dwblair/open-lab-monitor/pcb/reference/microsdbb_LRG.jpg

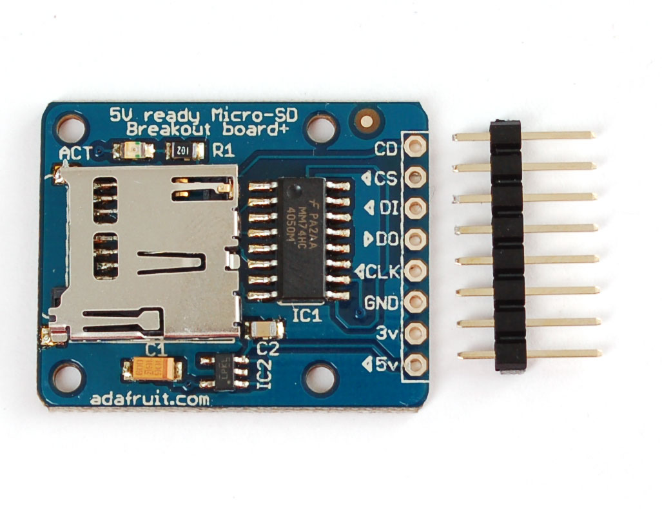
pcb/reference/microsdbb_LRG.jpg
