dwblair/open-lab-monitor/pcb/eagle/olm-base_v0.9brd.png

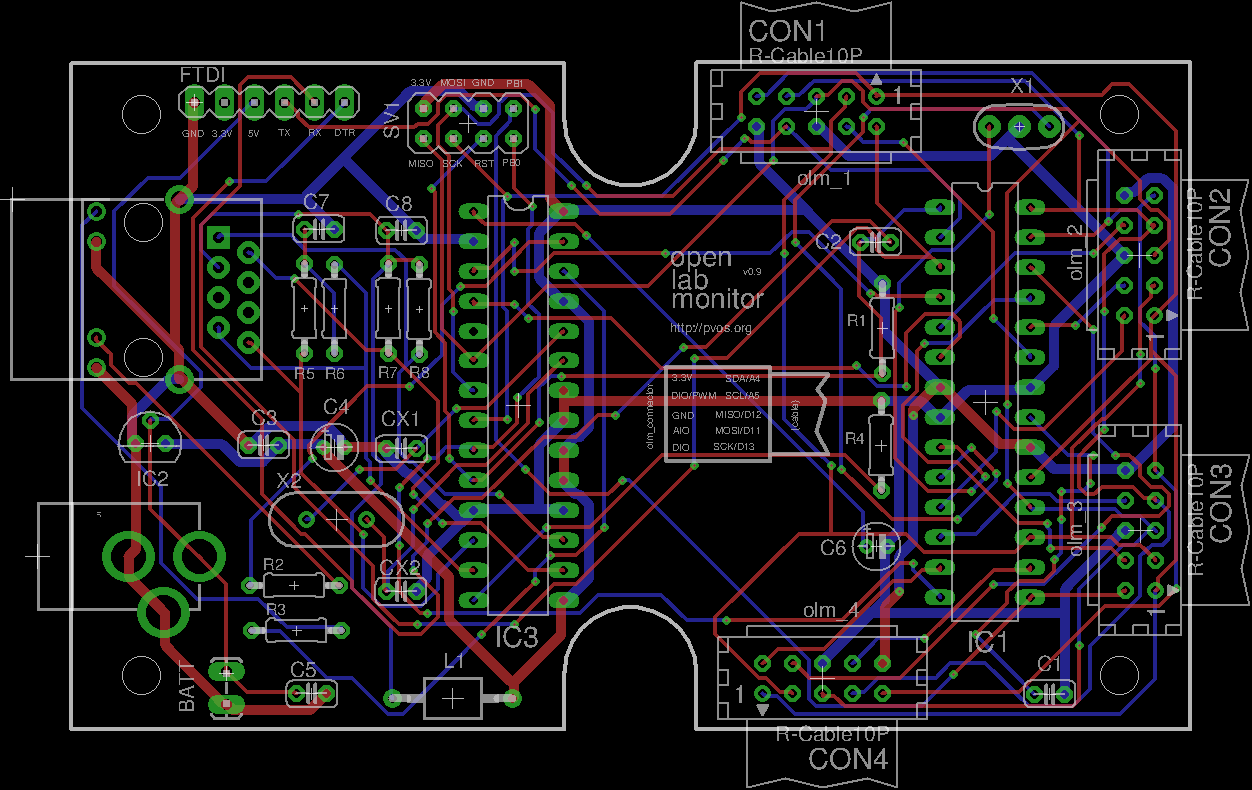
pcb/eagle/olm-base_v0.9brd.png
