dwblair/open-lab-monitor/pcb/eagle/olm-base_v0.9sch.png

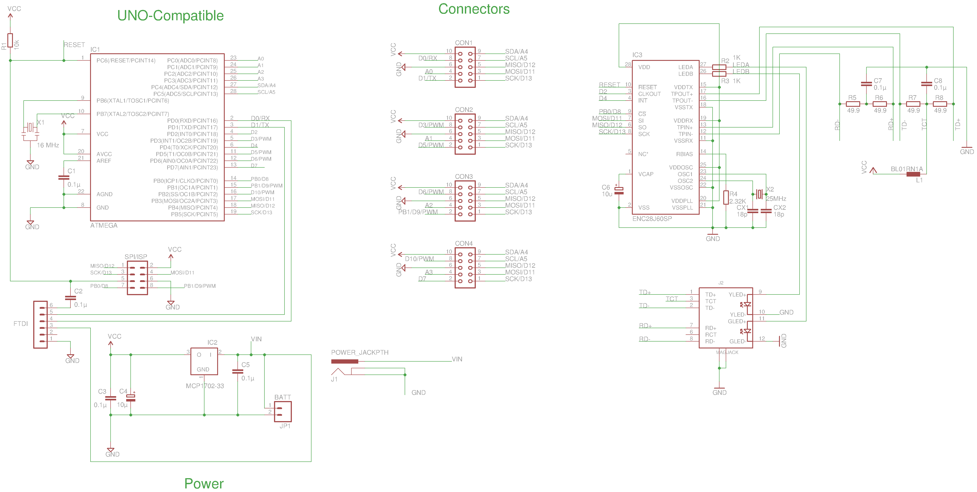
pcb/eagle/olm-base_v0.9sch.png
