dwblair/open-lab-monitor/pcb/eagle/OLM-base_v.9REVA.png

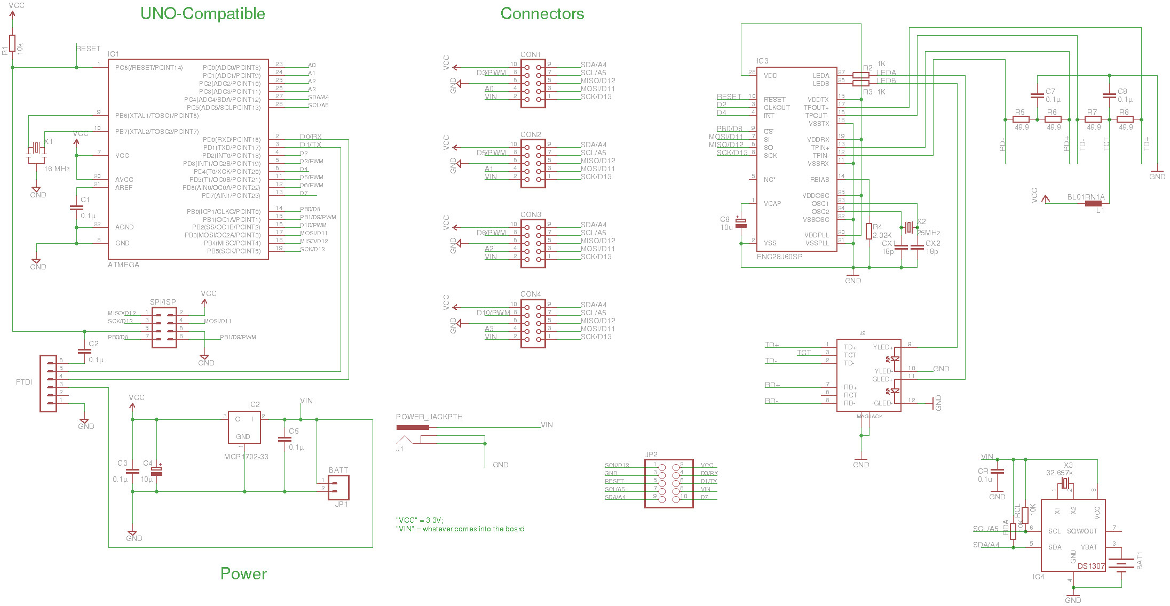
pcb/eagle/OLM-base_v.9REVA.png
