dwblair/open-lab-monitor/pcb/eagle/OLM-base_v.9REVAbrd.png

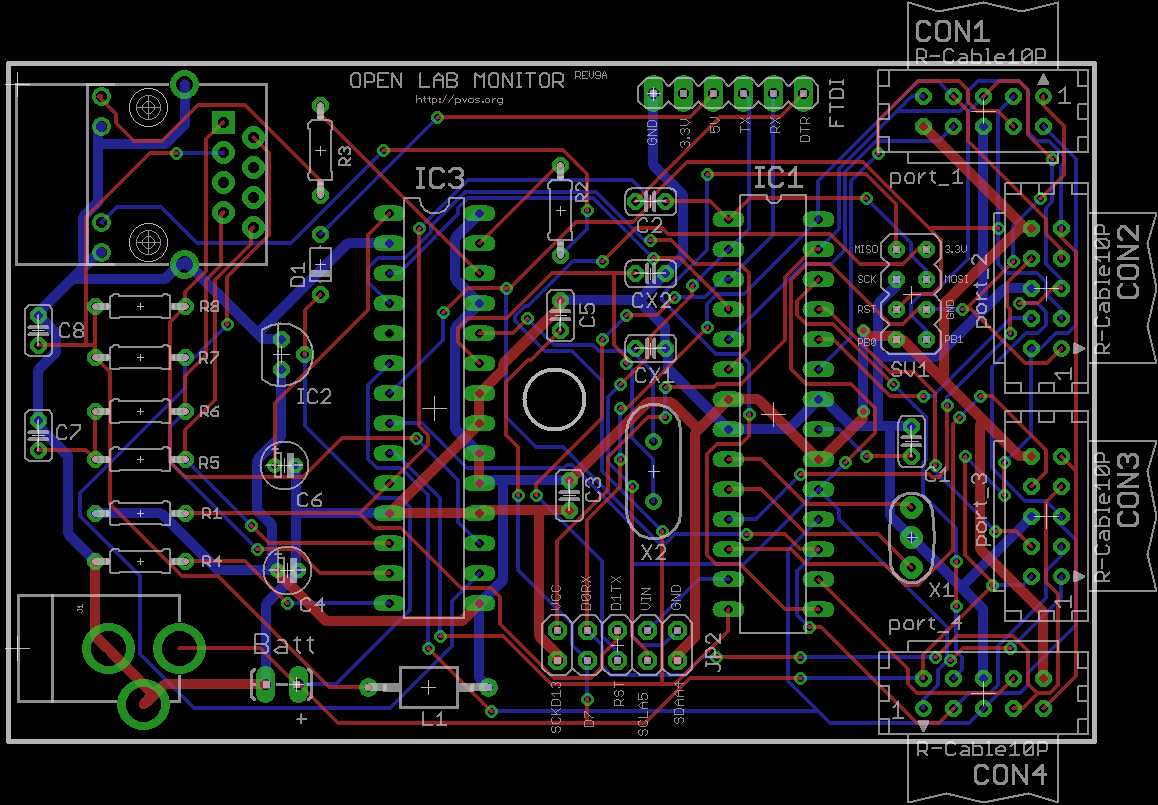
pcb/eagle/OLM-base_v.9REVAbrd.png
