dwblair/open-lab-monitor/pcb/eagle/OLM-base_v.9REVAsch.png

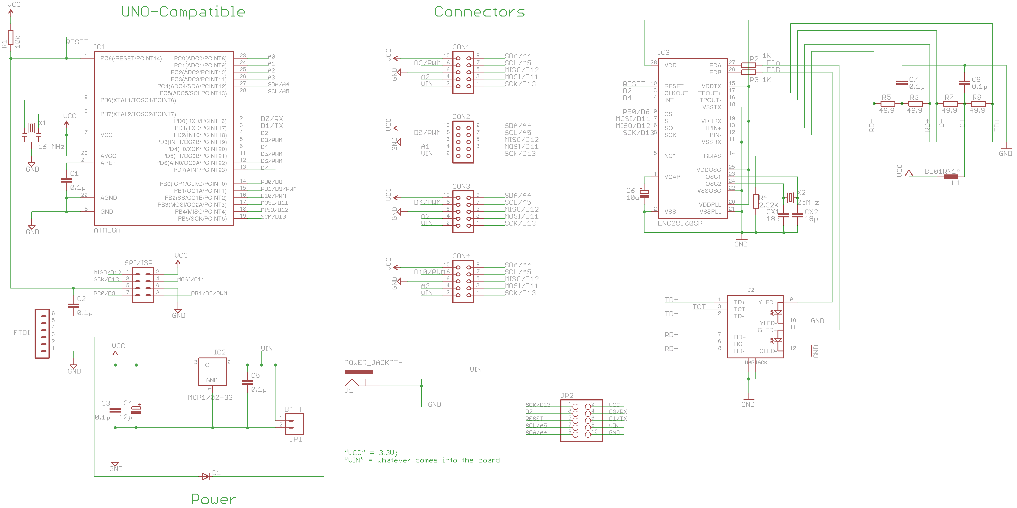
pcb/eagle/OLM-base_v.9REVAsch.png
