dwblair/open-lab-monitor/pcb/eagle/OLM-periph-prob+ambientsch.png

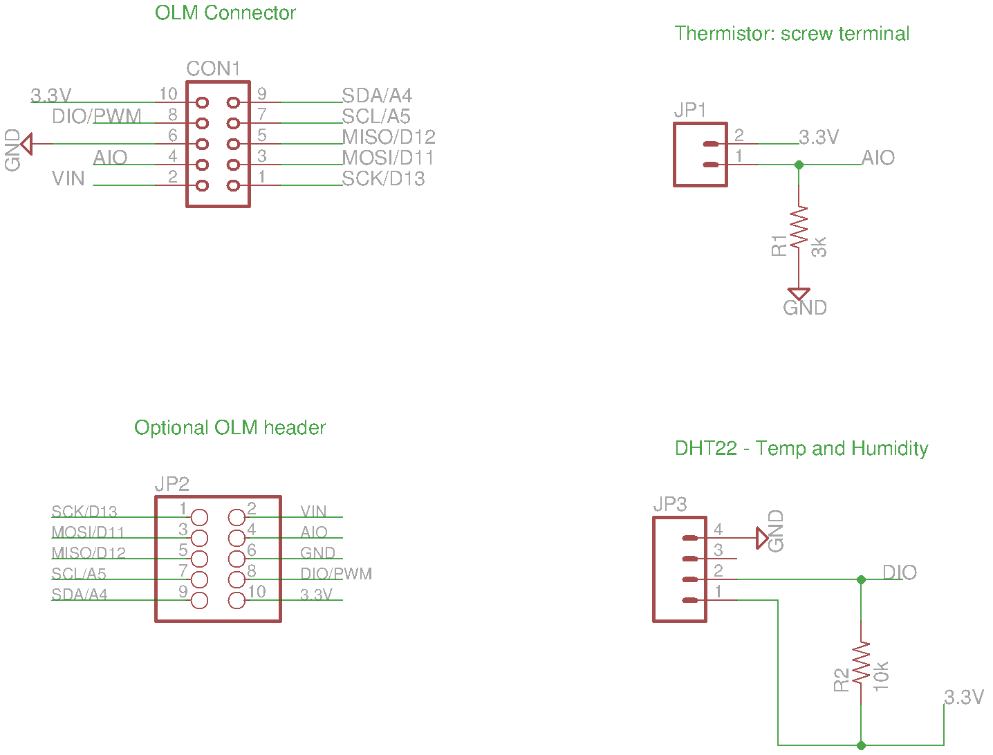
pcb/eagle/OLM-periph-prob+ambientsch.png
