dwblair/open-lab-monitor/pcb/eagle/olm-periph-probe+ambientREV9Abrd.png

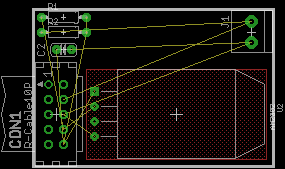
pcb/eagle/olm-periph-probe+ambientREV9Abrd.png
