dwblair/open-lab-monitor/pcb/geda/OLM-v5.png

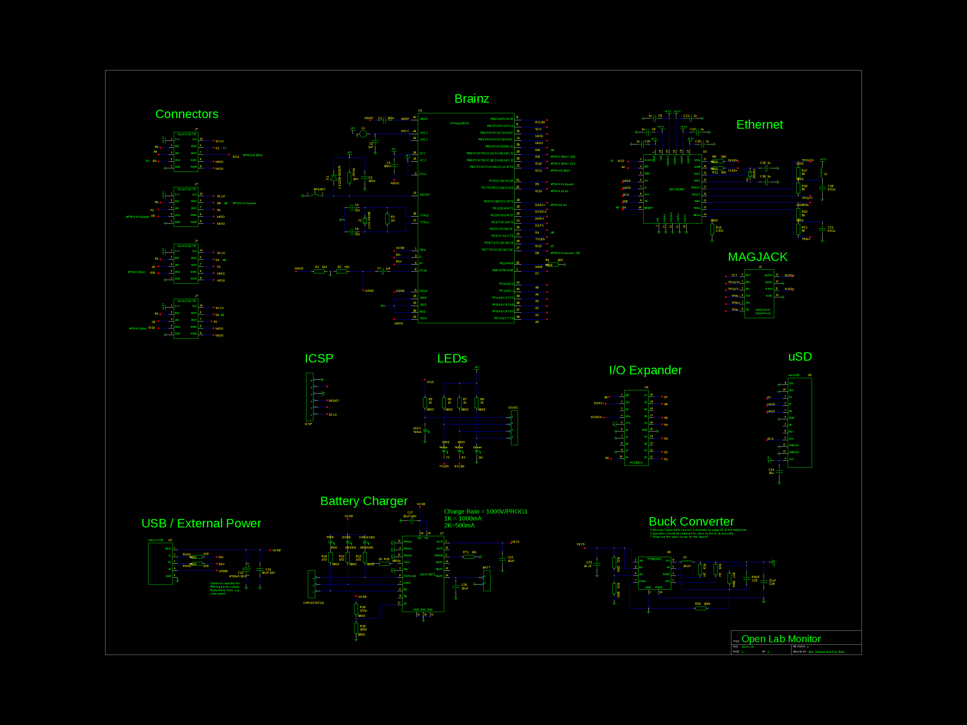
pcb/geda/OLM-v5.png
