dwblair/open-lab-monitor/pcb/reference/OLM.png

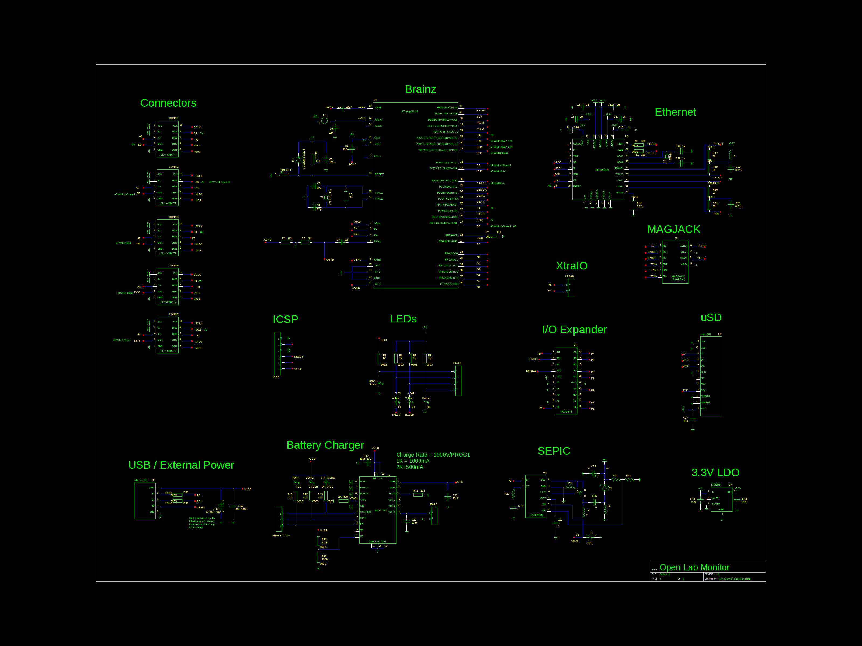
pcb/reference/OLM.png
