dwblair/open-lab-monitor/pcb/reference/olmetherv02.png

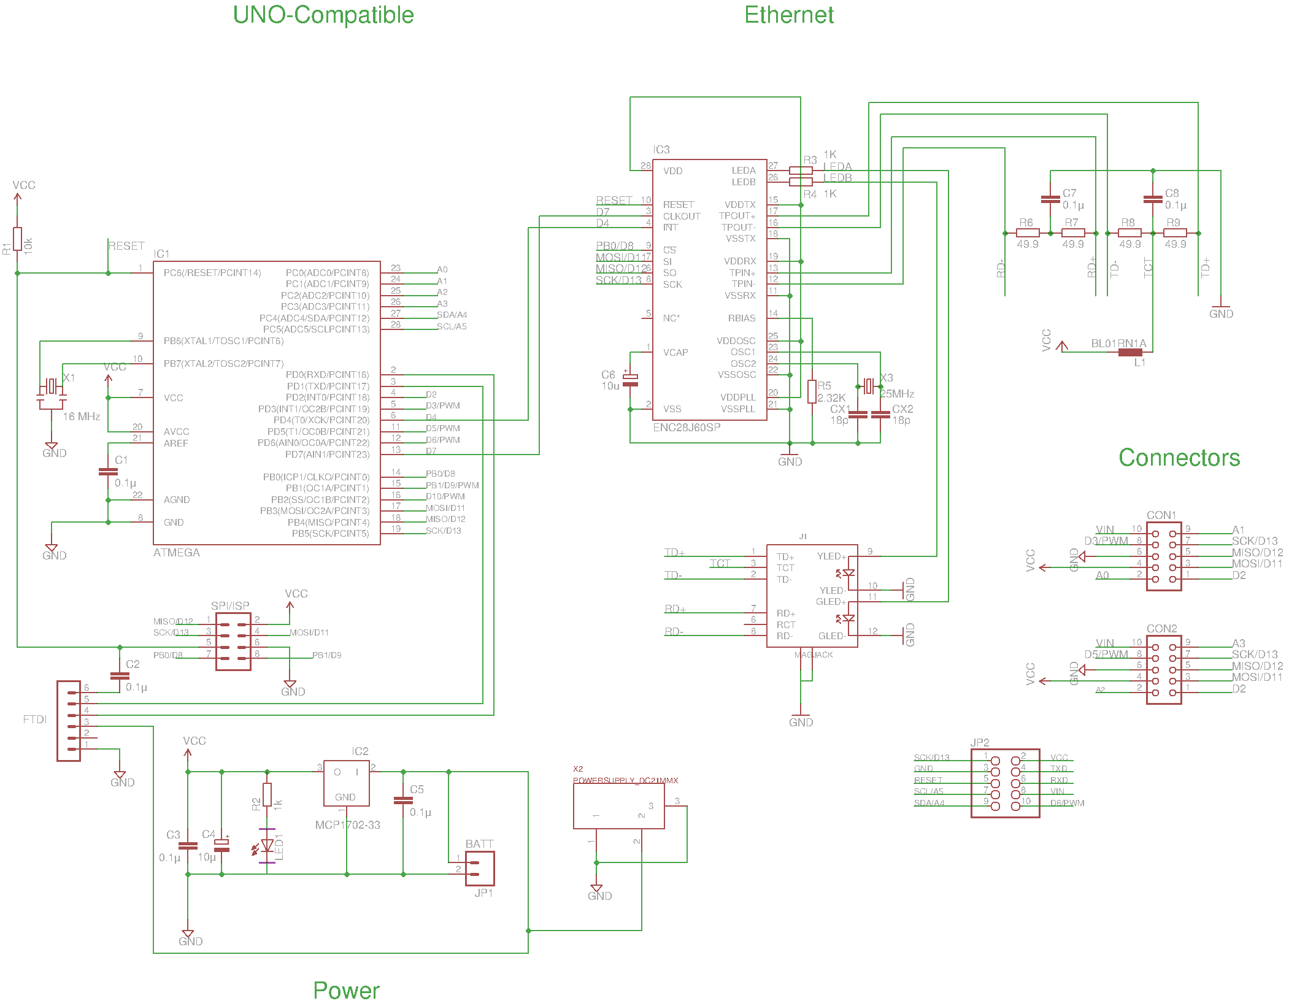
pcb/reference/olmetherv02.png
