dwblair/open-lab-monitor/docs/Arduino_Leonardo-REV3b.brd

## EAGLE design docs/Arduino_Leonardo-REV3b.brd (2013-01-09)

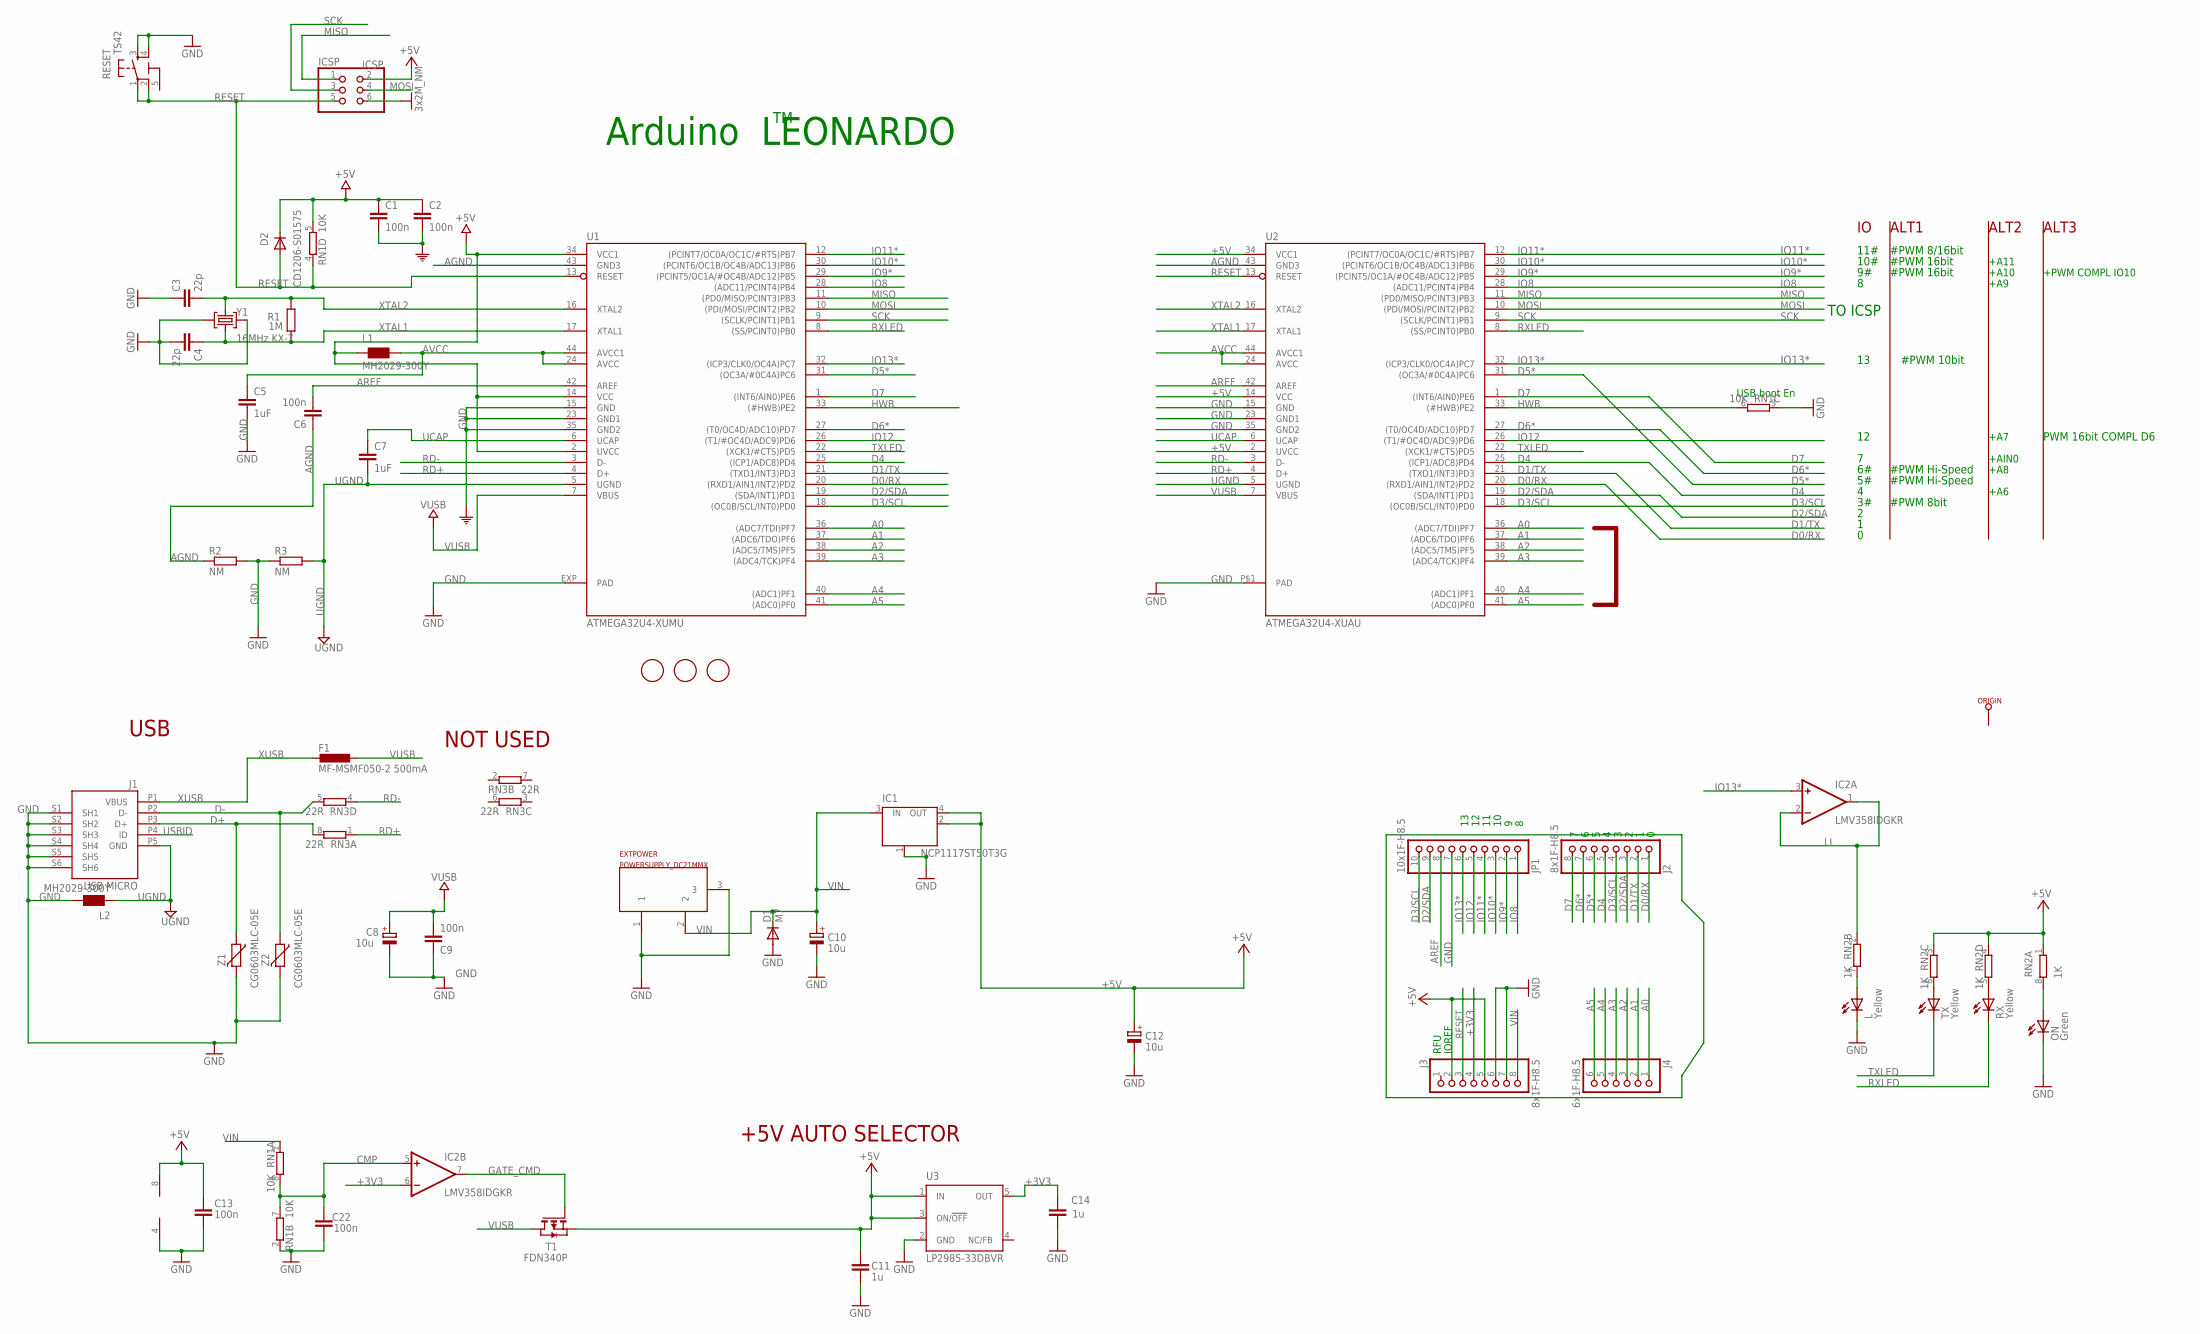
[picture p52: schematic Arduino_Leonardo-REV3b.sch]

Parts:
C1, C2, C6, C9, C13, C22: 100n; C0603-ROUND
C3, C4: 22p; C0603-ROUND
C5, C7: 1uF; C0603-ROUND
C8, C10, C12: 10u; SMC_B
C11, C14: 1u; C0603-ROUND
D1: M7; SMB
D2: CD1206-S01575; MINIMELF
EXTPOWER: POWERSUPPLY_DC21MMX; POWERSUPPLY_DC-21MM
F1: MF-MSMF050-2 500mA; L1812
FID1, FID2, FID3: FIDUCIALMOUNT; FIDUCIA-MOUNT
IC1: NCP1117ST50T3G; SOT223
IC2: LMV358IDGKR; MSOP08
ICSP: ICSP; 2X03
J1: USB MICRO; CON2_USB_MICRO_B_AT
J2, J3: 8x1F-H8.5; 1X08
J4: 6x1F-H8.5; 1X06
JP1: 10x1F-H8.5; 1X10
L: Yellow; CHIPLED_0805
L1, L2: MH2029-300Y; 0805
ON: Green; CHIPLED_0805
ORIGIN: TP_SP; TP-SP
R1: 1M; R0603-ROUND
R2, R3: NM; R0402
RESET: TS42
RN1: 10K; CAY16
RN2: 1K; CAY16
RN3: 22R; CAY16
RX: Yellow; CHIPLED_0805
T1: FDN340P; SOT-23
TX: Yellow; CHIPLED_0805
U1: ATMEGA32U4-XUMU; QFN44ML7X7
U2: ATMEGA32U4-XUAU; TQFP44-PAD
U3: LP2985-33DBVR; SOT23-DBV
Y1: 16MHz KX-7; CRYSTAL-3.2-2.5
Z1, Z2: CG0603MLC-05E; CT/CN0603

Connections:
5-GND: RESET.5 (5-GND)
+3V3: C14.2, IC2.6 (-IN), J3.4, U3.5 (OUT)
+5V: C1.1, C2.1, C11.2, C12.+, C13.1, D2.C, IC1.2 (OUT), IC1.4 (OUT), IC2.8 (V+), ICSP.2, J3.2, J3.5, L1.1, RN1.5 (2), RN2.1, RN2.3 (1), RN2.4 (1), T1.2 (S), U1.2 (UVCC), U1.14 (VCC), U1.34 (VCC1), U2.2 (UVCC), U2.14 (VCC), U2.34 (VCC1), U3.1 (IN), U3.3 (ON/!OFF)
A0: J4.1, U1.36 ((ADC7/TDI)PF7), U2.36 ((ADC7/TDI)PF7)
A1: J4.2, U1.37 ((ADC6/TDO)PF6), U2.37 ((ADC6/TDO)PF6)
A2: J4.3, U1.38 ((ADC5/TMS)PF5), U2.38 ((ADC5/TMS)PF5)
A3: J4.4, U1.39 ((ADC4/TCK)PF4), U2.39 ((ADC4/TCK)PF4)
A4: J4.5, U1.40 ((ADC1)PF1), U2.40 ((ADC1)PF1)
A5: J4.6, U1.41 ((ADC0)PF0), U2.41 ((ADC0)PF0)
AGND: C6.1, R2.1, U1.43 (GND3), U2.43 (GND3)
AREF: C6.2, JP1.8, U1.42 (AREF), U2.42 (AREF)
AVCC: C5.1, L1.2, U1.24 (AVCC), U1.44 (AVCC1), U2.24 (AVCC), U2.44 (AVCC1)
CMP: C22.2, IC2.5 (+IN), RN1.7 (2), RN1.8 (2)
D0/RX: J2.1, U1.20 ((RXD1/AIN1/INT2)PD2), U2.20 ((RXD1/AIN1/INT2)PD2)
D1/TX: J2.2, U1.21 ((TXD1/INT3)PD3), U2.21 ((TXD1/INT3)PD3)
D2/SDA: J2.3, JP1.9, U1.19 ((SDA/INT1)PD1), U2.19 ((SDA/INT1)PD1)
D3/SCL: J2.4, JP1.10, U1.18 ((OC0B/SCL/INT0)PD0), U2.18 ((OC0B/SCL/INT0)PD0)
D4: J2.5, U1.25 ((ICP1/ADC8)PD4), U2.25 ((ICP1/ADC8)PD4)
D5*: J2.6, U1.31 ((OC3A/#0C4A)PC6), U2.31 ((OC3A/#0C4A)PC6)
D6*: J2.7, U1.27 ((T0/OC4D/ADC10)PD7), U2.27 ((T0/OC4D/ADC10)PD7)
D7: J2.8, U1.1 ((INT6/AIN0)PE6), U2.1 ((INT6/AIN0)PE6)
D+: J1.P3 (D+), RN3.8 (2), Z1.1
D-: J1.P2 (D-), RN3.5 (2), Z2.1
GATE_CMD: IC2.7 (OUT), T1.3 (G)
GND: C1.2, C2.2, C3.1, C4.2, C5.2, C8.-, C9.1, C10.-, C11.1, C12.-, C13.2, C14.1, C22.1, D1.A, EXTPOWER.1, EXTPOWER.3, IC1.1 (GND/ADJ), IC2.4 (V-), ICSP.6, J1.S1 (SH1), J1.S2 (SH2), J1.S3 (SH3), J1.S4 (SH4), J1.S5 (SH5), J1.S6 (SH6), J3.6, J3.7, JP1.7, L.C, L2.2, ON.C, R2.2, R3.1, RESET.3, RESET.4, RN1.2 (1), RN1.3 (1), U1.15 (GND), U1.23 (GND1), U1.35 (GND2), U1.EXP (PAD), U2.15 (GND), U2.23 (GND1), U2.35 (GND2), U2.P$1 (PAD), U3.2 (GND), Y1.2 (GND), Y1.4 (GND), Z1.2, Z2.2
HWB: RN1.6 (2), U1.33 ((#HWB)PE2), U2.33 ((#HWB)PE2)
IO8: JP1.1, U1.28 ((ADC11/PCINT4)PB4), U2.28 ((ADC11/PCINT4)PB4)
IO9*: JP1.2, U1.29 ((PCINT5/OC1A/#OC4B/ADC12)PB5), U2.29 ((PCINT5/OC1A/#OC4B/ADC12)PB5)
IO10*: JP1.3, U1.30 ((PCINT6/OC1B/OC4B/ADC13)PB6), U2.30 ((PCINT6/OC1B/OC4B/ADC13)PB6)
IO11*: JP1.4, U1.12 ((PCINT7/OC0A/OC1C/#RTS)PB7), U2.12 ((PCINT7/OC0A/OC1C/#RTS)PB7)
IO12: JP1.5, U1.26 ((T1/#OC4D/ADC9)PD6), U2.26 ((T1/#OC4D/ADC9)PD6)
IO13*: IC2.3 (+IN), JP1.6, U1.32 ((ICP3/CLK0/OC4A)PC7), U2.32 ((ICP3/CLK0/OC4A)PC7)
LL: IC2.1 (OUT), IC2.2 (-IN), RN2.2 (1)
MISO: ICSP.1, U1.11 ((PD0/MISO/PCINT3)PB3), U2.11 ((PD0/MISO/PCINT3)PB3)
MOSI: ICSP.4, U1.10 ((PDI/MOSI/PCINT2)PB2), U2.10 ((PDI/MOSI/PCINT2)PB2)
unnamed: L.A, RN2.7 (2)
unnamed: ON.A, RN2.8 (2)
unnamed: RN2.6 (2), TX.A
unnamed: RN2.5 (2), RX.A
RD+: RN3.1, U1.4 (D+), U2.4 (D+)
RD-: RN3.4 (1), U1.3 (D-), U2.3 (D-)
RESET: D2.A, ICSP.5, J3.3, RESET.1, RESET.2, RN1.4 (1), U1.13 (RESET), U2.13 (RESET)
RXLED: RX.C, U1.8 ((SS/PCINT0)PB0), U2.8 ((SS/PCINT0)PB0)
SCK: ICSP.3, U1.9 ((SCLK/PCINT1)PB1), U2.9 ((SCLK/PCINT1)PB1)
TXLED: TX.C, U1.22 ((XCK1/#CTS)PD5), U2.22 ((XCK1/#CTS)PD5)
UCAP: C7.1, U1.6 (UCAP), U2.6 (UCAP)
UGND: C7.2, J1.P5 (GND), L2.1, R3.2, U1.5 (UGND), U2.5 (UGND)
USBID: J1.P4 (ID)
VIN: C10.+, D1.C, EXTPOWER.2, IC1.3 (IN), J3.8, RN1.1
VUSB: C8.+, C9.2, F1.1, T1.1 (D), U1.7 (VBUS), U2.7 (VBUS)
XTAL1: C4.1, R1.1, U1.17 (XTAL1), U2.17 (XTAL1), Y1.1 (C1)
XTAL2: C3.2, R1.2, U1.16 (XTAL2), U2.16 (XTAL2), Y1.3 (C2)
XUSB: F1.2, J1.P1 (VBUS)

Notes on the sheet:
Arduino LEONARDO
USB boot En
USB
+5V AUTO SELECTOR
NOT USED
TO ICSP
10#
11#
#PWM 8bit
#PWM Hi-Speed
#PWM 8/16bit
#PWM 16bit
PWM 16bit COMPL D6
#PWM 10bit
+A6
+A7
IOREF
RFU
+A11
+A10
+A8
+A9
+PWM COMPL IO10
+AIN0
ALT1
ALT2
ALT3

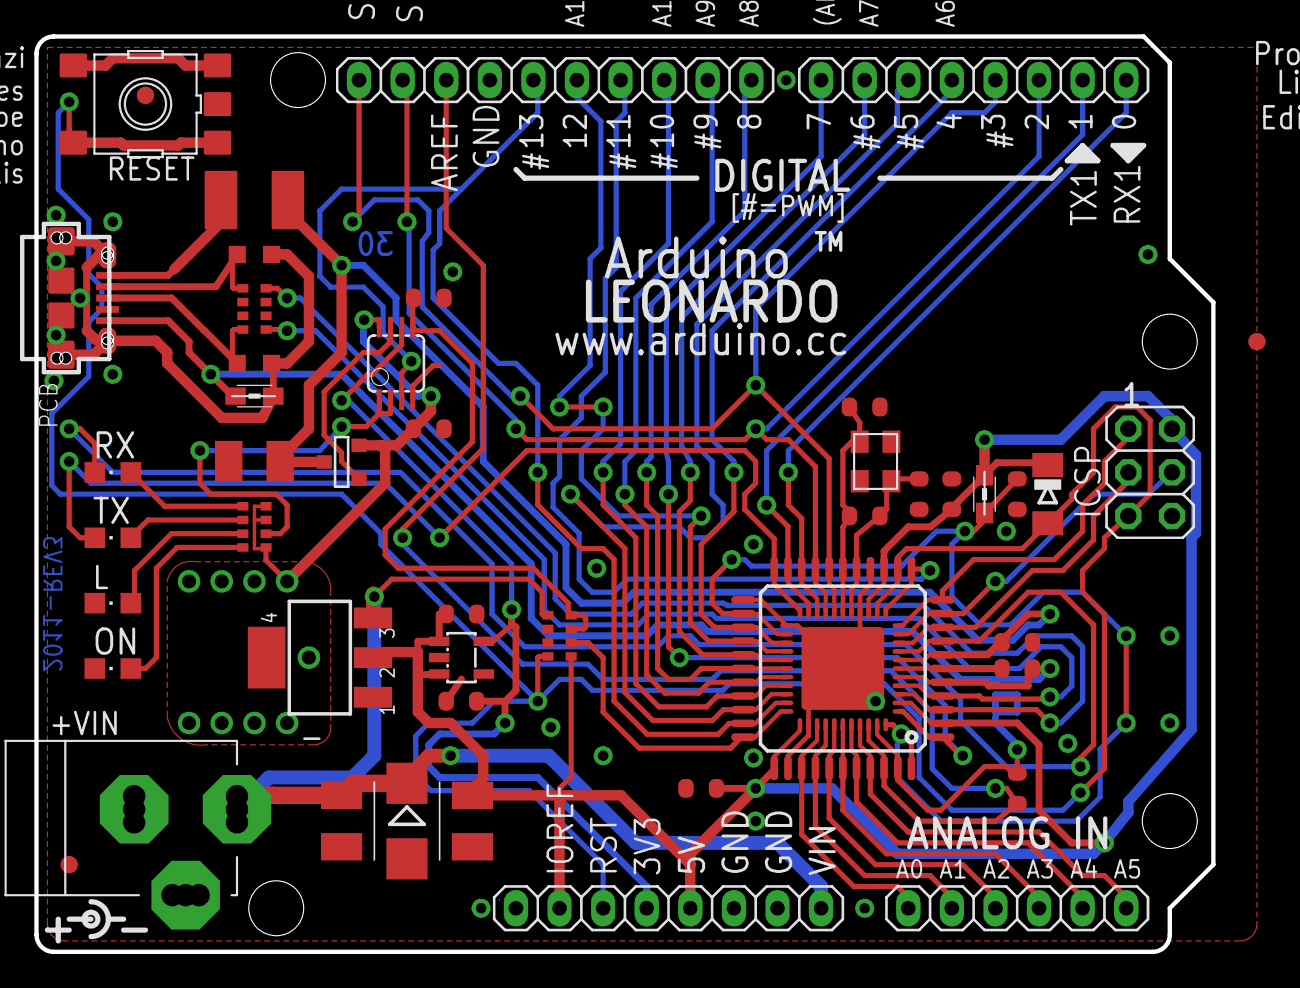
[picture p53: board Arduino_Leonardo-REV3b.brd from above]

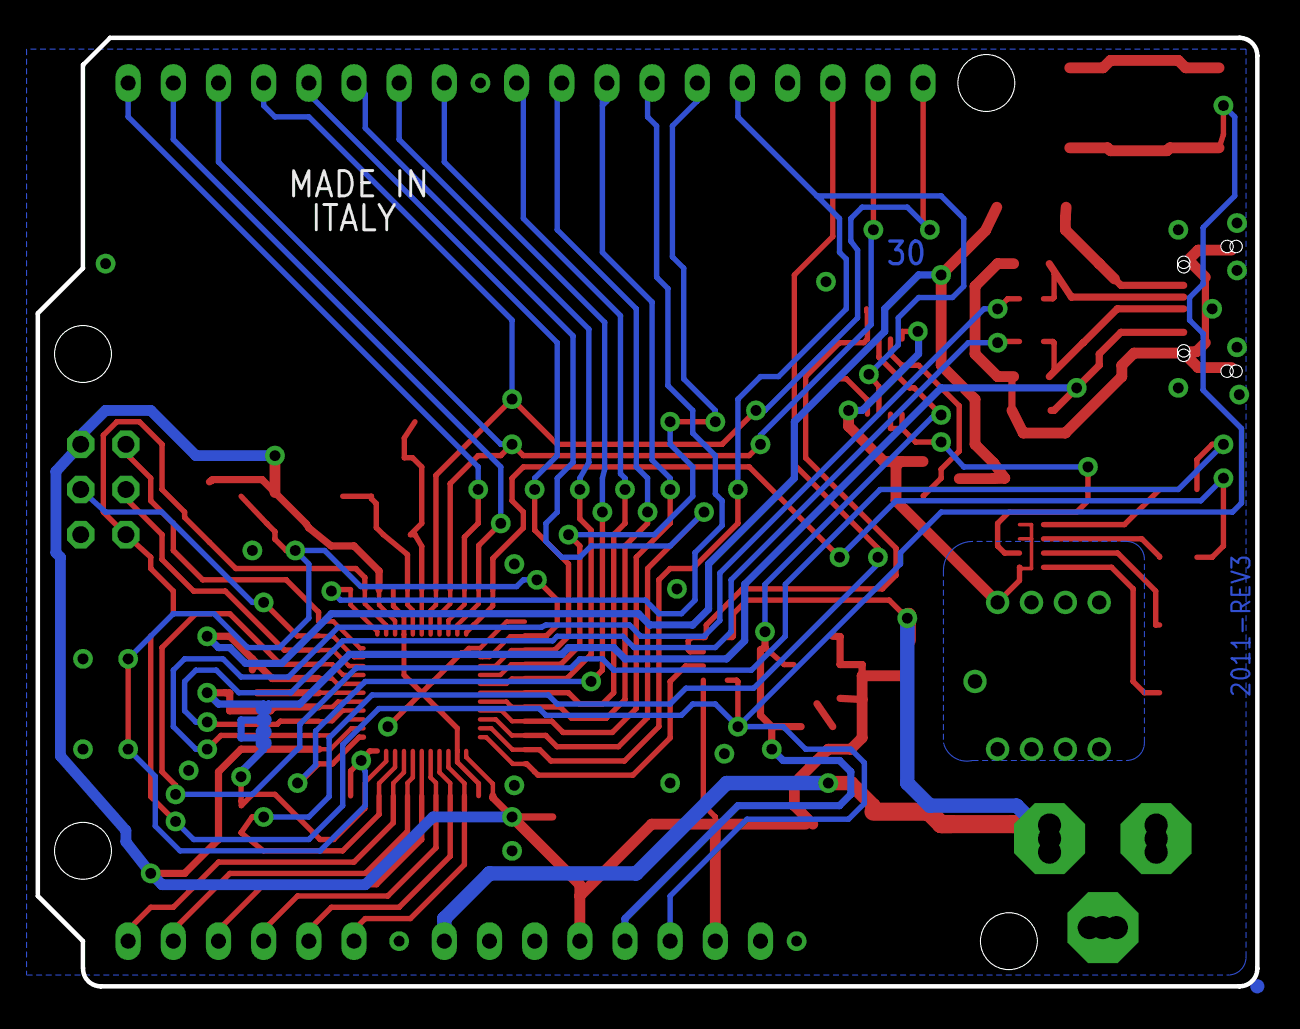
[picture p54: board Arduino_Leonardo-REV3b.brd from below]

Board: 2 copper layers, 68.6 x 53.3 mm, 51 parts (2 on the bottom side), 51 nets.
